lukasznowarkiewicz/Emersense/Hardware-mechanical/car_lighter_port_version/do zapalniczki rev1_00004.tif

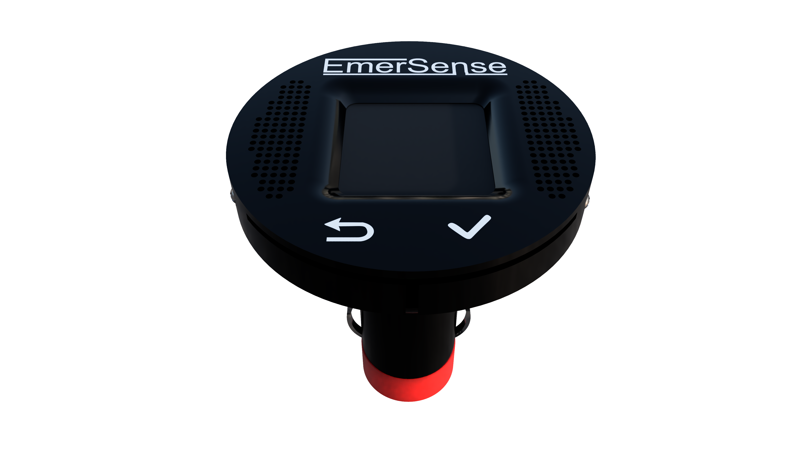
Hardware-mechanical/car_lighter_port_version/do zapalniczki rev1_00004.tif
