lukasznowarkiewicz/Emersense/Hardware-mechanical/car_lighter_port_version/do zapalniczki rev1_00015.tif

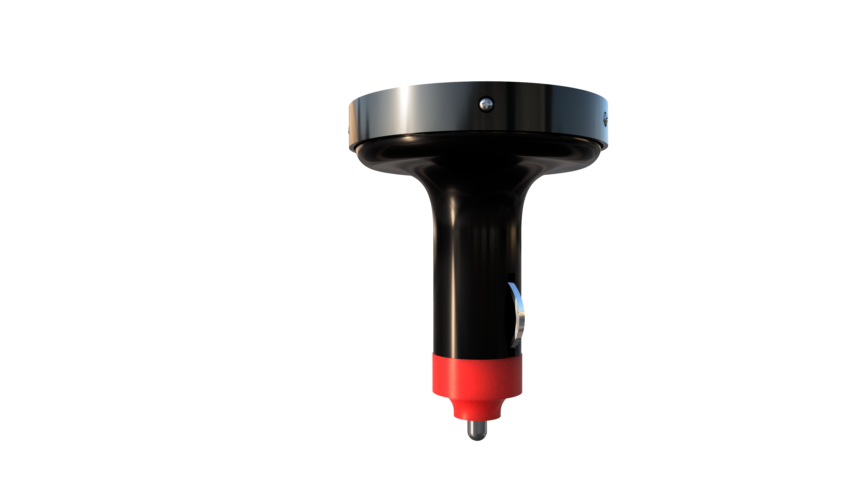
Hardware-mechanical/car_lighter_port_version/do zapalniczki rev1_00015.tif
