lukasznowarkiewicz/Emersense/Hardware-mechanical/car_lighter_port_version/Screenshot 2021-10-23 at 14.42.17.png

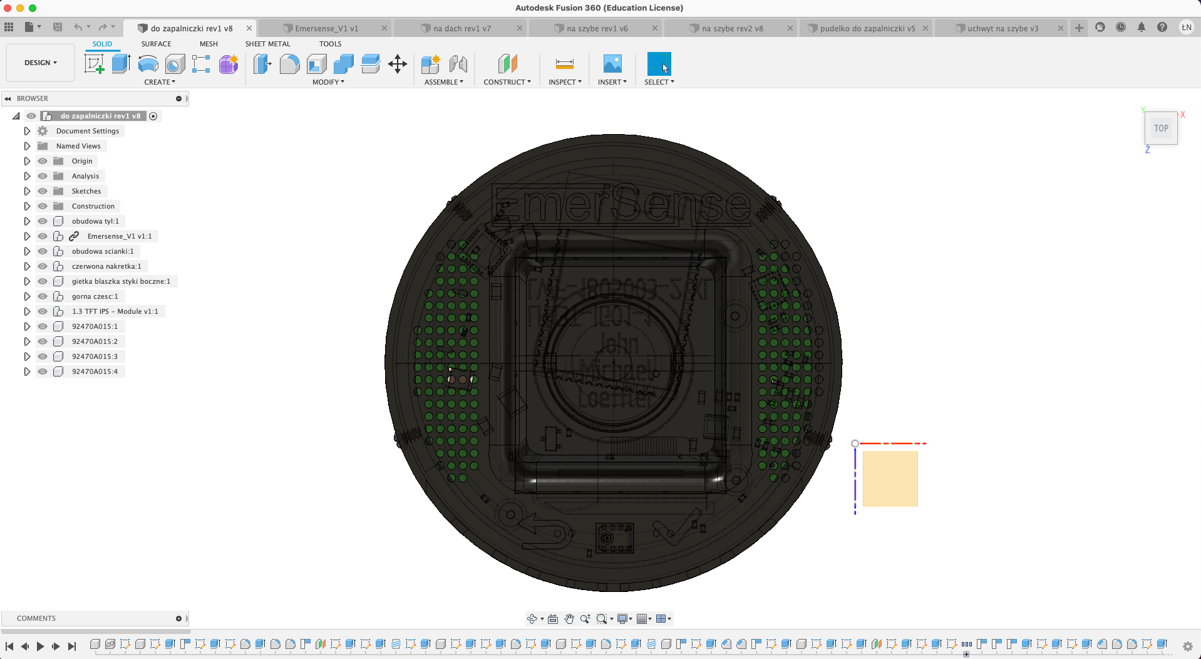
Hardware-mechanical/car_lighter_port_version/Screenshot 2021-10-23 at 14.42.17.png
