lukasznowarkiewicz/Emersense/Hardware-mechanical/roof_module/na_dach_rev1_00002.tif

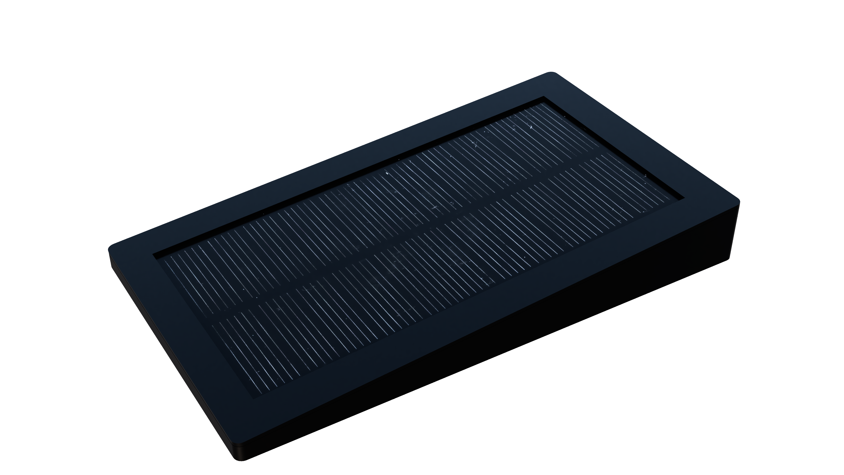
Hardware-mechanical/roof_module/na_dach_rev1_00002.tif
