lukasznowarkiewicz/Emersense/Hardware-mechanical/roof_module/na_dach_rev1_00003.tif

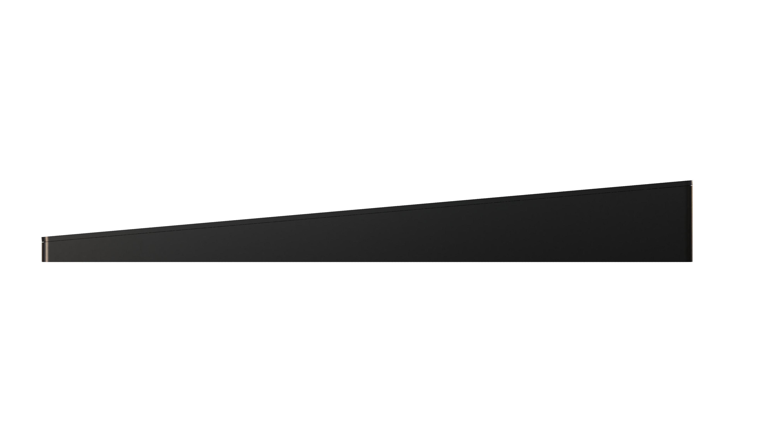
Hardware-mechanical/roof_module/na_dach_rev1_00003.tif
