lukasznowarkiewicz/Emersense/Hardware-mechanical/roof_module/na_dach_rev1_00005.tif

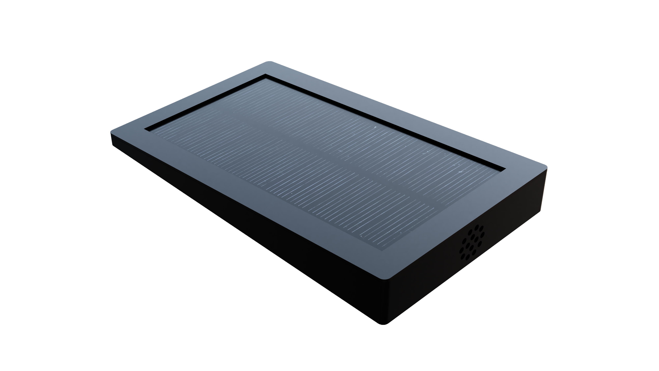
Hardware-mechanical/roof_module/na_dach_rev1_00005.tif
