lukasznowarkiewicz/Emersense/Hardware-mechanical/roof_module/na_dach_rev1_00013.tif

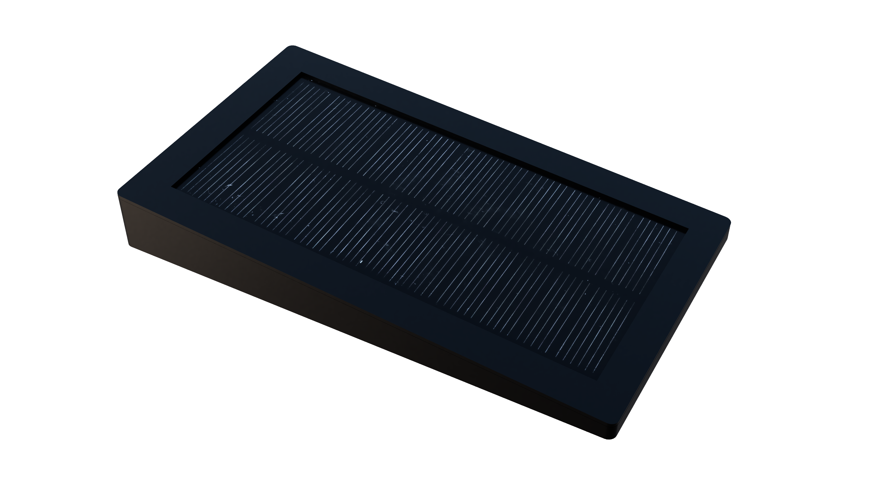
Hardware-mechanical/roof_module/na_dach_rev1_00013.tif
