lukasznowarkiewicz/Emersense/Hardware-mechanical/roof_module/na_dach_rev1_00014.tif

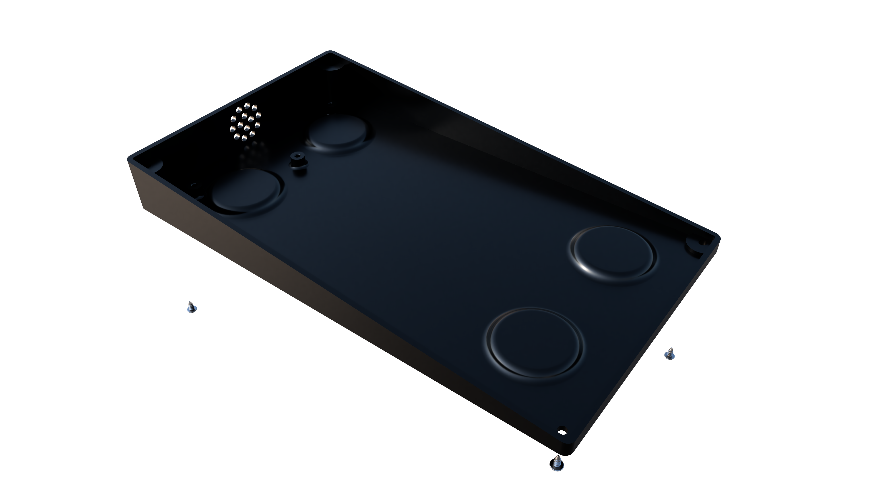
Hardware-mechanical/roof_module/na_dach_rev1_00014.tif
