lukasznowarkiewicz/Emersense/Hardware-mechanical/roof_module/Screenshot 2021-10-23 at 14.44.05.png

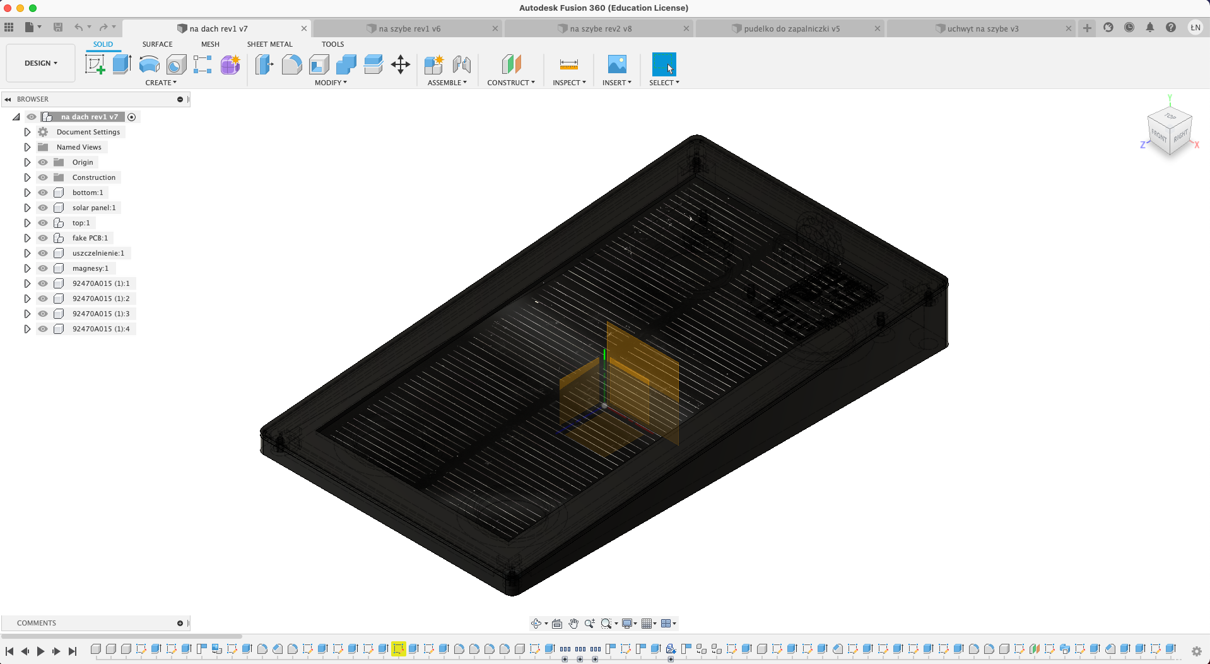
Hardware-mechanical/roof_module/Screenshot 2021-10-23 at 14.44.05.png
