lukasznowarkiewicz/Emersense/Hardware-mechanical/roof_module/Screenshot 2021-10-23 at 14.45.07.png

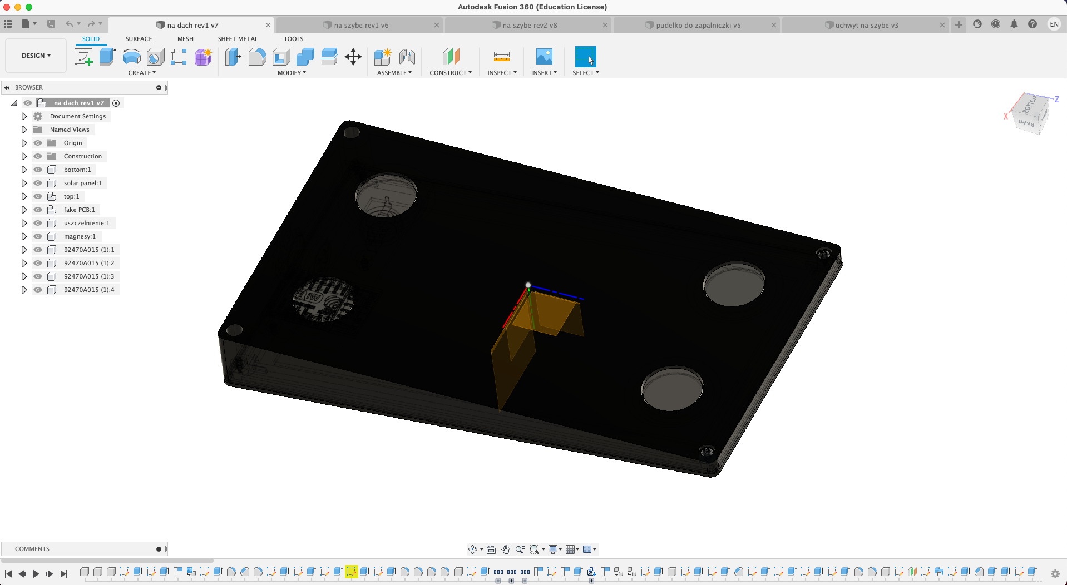
Hardware-mechanical/roof_module/Screenshot 2021-10-23 at 14.45.07.png
