lukasznowarkiewicz/Emersense/Hardware-mechanical/windshield_version/na_szybe_rev1_00031.tif

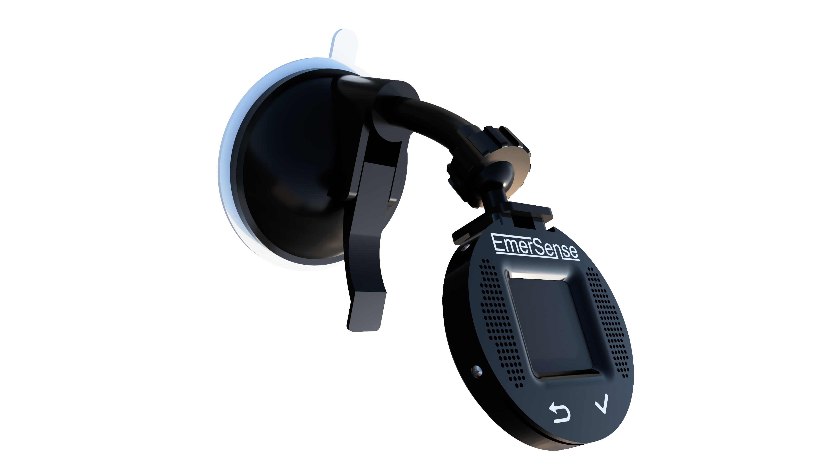
Hardware-mechanical/windshield_version/na_szybe_rev1_00031.tif
