lukasznowarkiewicz/Emersense/Hardware-mechanical/windshield_version/Screenshot 2021-10-23 at 14.45.29.png

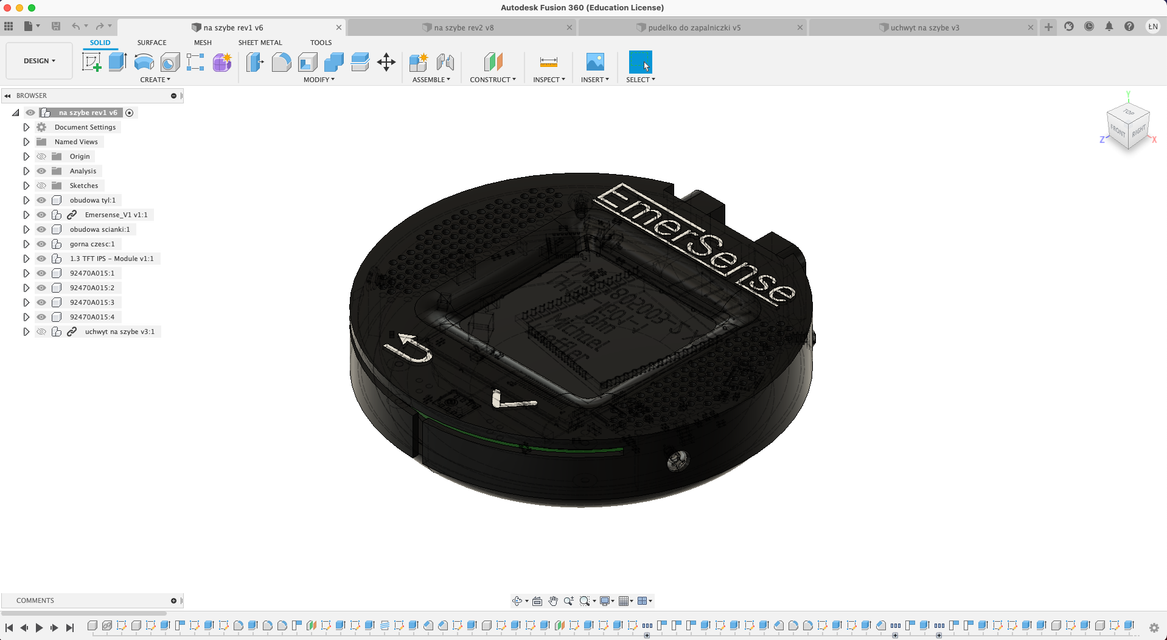
Hardware-mechanical/windshield_version/Screenshot 2021-10-23 at 14.45.29.png
