lukasznowarkiewicz/Emersense/imagesAndVideos/emersense_fusion360.png

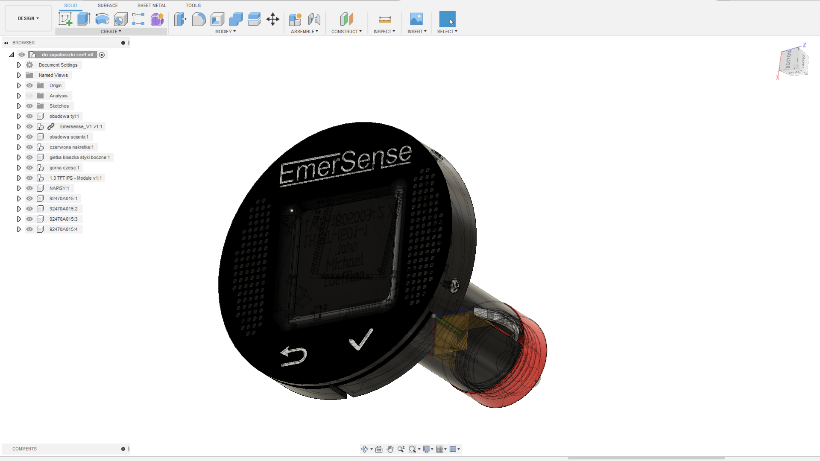
imagesAndVideos/emersense_fusion360.png
