lukasznowarkiewicz/Emersense/imagesAndVideos/emersense_pcb_bottom.jpeg

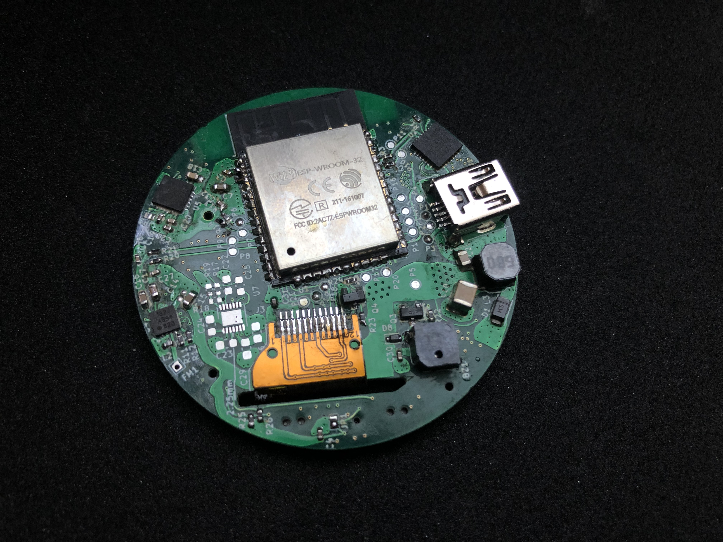
imagesAndVideos/emersense_pcb_bottom.jpeg
