lukasznowarkiewicz/Emersense/imagesAndVideos/emersense_pcb_top.jpeg

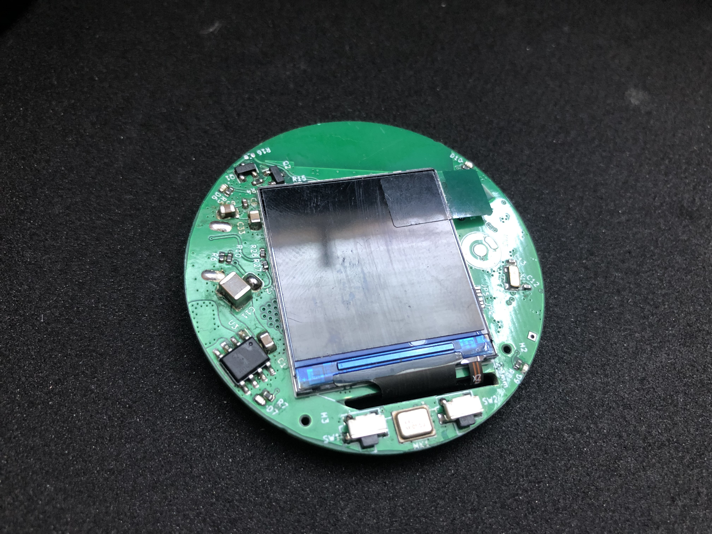
imagesAndVideos/emersense_pcb_top.jpeg
