lukasznowarkiewicz/Emersense/Hardware-mechanical/windshield_version/assembly renders/na_szybe_rev1_2021-May-31_08-34-41PM-000_CustomizedView7703543968.tif

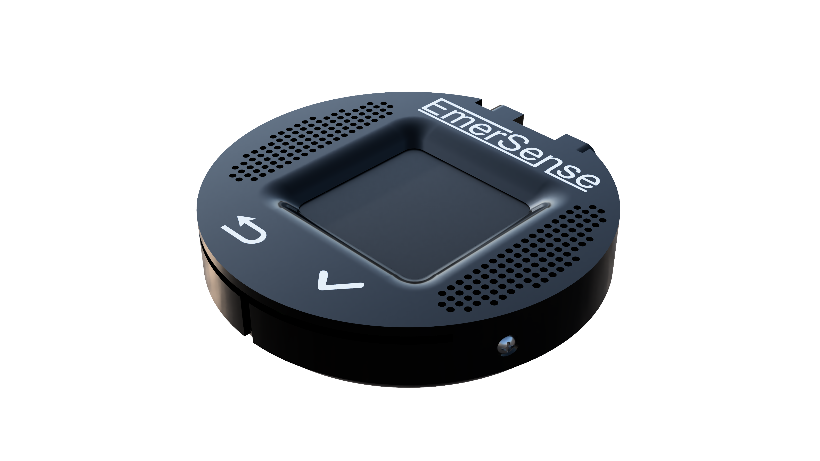
Hardware-mechanical/windshield_version/assembly renders/na_szybe_rev1_2021-May-31_08-34-41PM-000_CustomizedView7703543968.tif
